tchristle/e-cribbage/Software/MSP430 - C examples/msp430x20x2_adc10_01.c

//******************************************************************************
//  MSP430F20x2 Demo - ADC10, Sample A1, AVcc Ref, Set P1.0 if > 0.5*AVcc
//
//  Description: A single sample is made on A1 with reference to AVcc.
//  Software sets ADC10SC to start sample and conversion - ADC10SC
//  automatically cleared at EOC. ADC10 internal oscillator times sample (16x)
//  and conversion. In Mainloop MSP430 waits in LPM0 to save power until ADC10
//  conversion complete, ADC10_ISR will force exit from LPM0 in Mainloop on
//  reti. If A1 > 0.5*AVcc, P1.0 set, else reset.
//
//                MSP430F20x2
//             -----------------
//         /|\|              XIN|-
//          | |                 |
//          --|RST          XOUT|-
//            |                 |
//        >---|P1.1/A1      P1.0|-->LED
//
//  L. Westlund
//  Texas Instruments Inc.
//  May 2006
//  Built with CCE Version: 3.2.0 and IAR Embedded Workbench Version: 3.41A
//******************************************************************************
#include "msp430x20x2.h"

void main(void)
{
  WDTCTL = WDTPW + WDTHOLD;                 // Stop WDT
  ADC10CTL0 = ADC10SHT_2 + ADC10ON + ADC10IE; // ADC10ON, interrupt enabled
  ADC10CTL1 = INCH_1;                       // input A1
  ADC10AE0 |= 0x02;                         // PA.1 ADC option select
  P1DIR |= 0x01;                            // Set P1.0 to output direction

  for (;;)
  {
    ADC10CTL0 |= ENC + ADC10SC;             // Sampling and conversion start
    __bis_SR_register(CPUOFF + GIE);        // LPM0, ADC10_ISR will force exit
    if (ADC10MEM < 0x1FF)
      P1OUT &= ~0x01;                       // Clear P1.0 LED off
    else
      P1OUT |= 0x01;                        // Set P1.0 LED on
  }
}

// ADC10 interrupt service routine
#pragma vector=ADC10_VECTOR
__interrupt void ADC10_ISR(void)
{
  __bic_SR_register_on_exit(CPUOFF);        // Clear CPUOFF bit from 0(SR)
}
