tchristle/e-cribbage/Software/MSP430 - C examples/msp430x20x3_1.c

//******************************************************************************
//  MSP430F20xx Demo - Software Toggle P1.0
//
//  Description; Toggle P1.0 by xor'ing P1.0 inside of a software loop.
//  ACLK = n/a, MCLK = SMCLK = default DCO
//
//                MSP430F20xx
//             -----------------
//         /|\|              XIN|-
//          | |                 |
//          --|RST          XOUT|-
//            |                 |
//            |             P1.0|-->LED
//
//  M.Buccini / L. Westlund
//  Texas Instruments, Inc
//  October 2005
//  Built with CCE Version: 3.2.0 and IAR Embedded Workbench Version: 3.40A
//******************************************************************************

#include  <msp430x20x3.h>

void main(void)
{
  WDTCTL = WDTPW + WDTHOLD;                 // Stop watchdog timer
  P1DIR |= 0x01;                            // Set P1.0 to output direction

  for (;;)
  {
    volatile unsigned int i;

    P1OUT ^= 0x01;                          // Toggle P1.0 using exclusive-OR

    i = 50000;                              // Delay
    do (i--);
    while (i != 0);
  }
}
