tchristle/e-cribbage/Software/MSP430 - C examples/msp430x20x3_P1_02.c

//******************************************************************************
//  MSP430F20xx Demo - Software Port Interrupt Service on P1.4 from LPM4
//
//  Description: A hi/low transition on P1.4 will trigger P1_ISR which,
//  toggles P1.0. Normal mode is LPM4 ~ 0.1uA. LPM4 current can be measured
//  with the LED removed, all unused P1.x/P2.x configured as output or inputs
//  pulled high or low, and ensure the P1.4 interrupt input does not float.
//  ACLK = n/a, MCLK = SMCLK = default DCO
//
//               MSP430F20xx
//            -----------------
//        /|\|              XIN|-
//         | |                 |
//         --|RST          XOUT|-
//     /|\   |                 |
//      --o--|P1.4         P1.0|-->LED
//     \|/
//
//  M.Buccini / L. Westlund
//  Texas Instruments, Inc
//  October 2005
//  Built with CCE Version: 3.2.0 and IAR Embedded Workbench Version: 3.40A
//******************************************************************************

#include  <msp430x20x3.h>

void main(void)
{
  WDTCTL = WDTPW + WDTHOLD;                 // Stop watchdog timer
  P1DIR |= 0x01;                            // Set P1.0 to output direction
  P1IE |= 0x10;                             // P1.4 interrupt enabled
  P1IES |= 0x10;                            // P1.4 Hi/lo edge
  P1IFG &= ~0x10;                           // P1.4 IFG cleared

  _BIS_SR(LPM4_bits + GIE);                 // Enter LPM4 w/interrupt
}

// Port 1 interrupt service routine
#pragma vector=PORT1_VECTOR
__interrupt void Port_1(void)
{
  P1OUT ^= 0x01;                            // P1.0 = toggle
  P1IFG &= ~0x10;                           // P1.4 IFG cleared
}
