tchristle/e-cribbage/Software/MSP430 - C examples/msp430x20x3_ta_03.c

//******************************************************************************
//  MSP430F20xx Demo - Timer_A, Toggle P1.0, Overflow ISR, DCO SMCLK
//
//  Description: Toggle P1.0 using software and Timer_A overflow ISR.
//  In this example an ISR triggers when TA overflows. Inside the TA
//  overflow ISR P1.0 is toggled. Toggle rate is approximatlely 12Hz.
//  Proper use of TAIV interrupt vector generator is demonstrated.
//  ACLK = n/a, MCLK = SMCLK = TACLK = default DCO
//
//           MSP430F20xx
//         ---------------
//     /|\|            XIN|-
//      | |               |
//      --|RST        XOUT|-
//        |               |
//        |           P1.0|-->LED
//
//  M. Buccini / L. Westlund
//  Texas Instruments Inc.
//  October 2005
//  Built with CCE Version: 3.2.0 and IAR Embedded Workbench Version: 3.40A
//******************************************************************************

#include <msp430x20x3.h>

void main(void)
{
  WDTCTL = WDTPW + WDTHOLD;                 // Stop WDT
  P1DIR |= 0x01;                            // P1.0 output
  TACTL = TASSEL_2 + MC_2 + TAIE;           // SMCLK, contmode, interrupt

  _BIS_SR(LPM0_bits + GIE);                 // Enter LPM0 w/ interrupt
}

// Timer_A3 Interrupt Vector (TAIV) handler
#pragma vector=TIMERA1_VECTOR
__interrupt void Timer_A(void)
{
 switch( TAIV )
 {
   case  2: break;                          // CCR1 not used
   case  4: break;                          // CCR2 not used
   case 10: P1OUT ^= 0x01;                  // overflow
            break;
 }
}
